jimrushPersonal/3D-Printed-Walkway-Lantern/docs/images/Bulk_Production.jpg

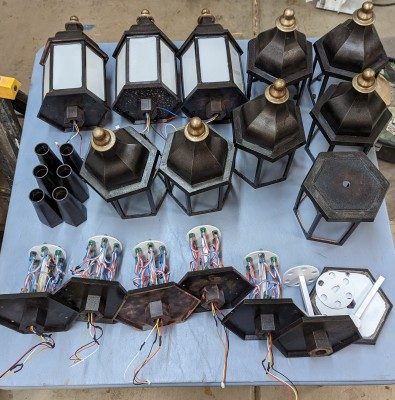
docs/images/Bulk_Production.jpg
