jimrushPersonal/3D-Printed-Walkway-Lantern/Post Ideas/complex post.PNG

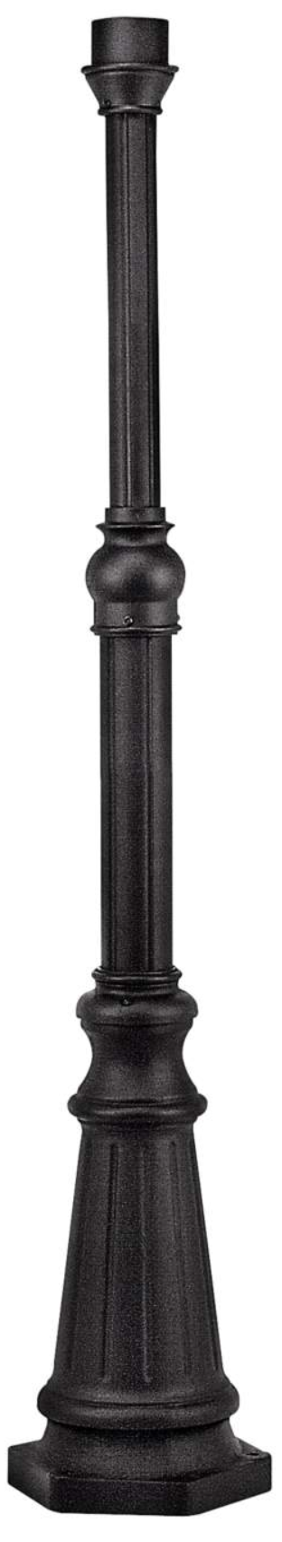
Post Ideas/complex post.PNG
